BarbodH/ampere/components/chassis/v1.1/chassis.stl

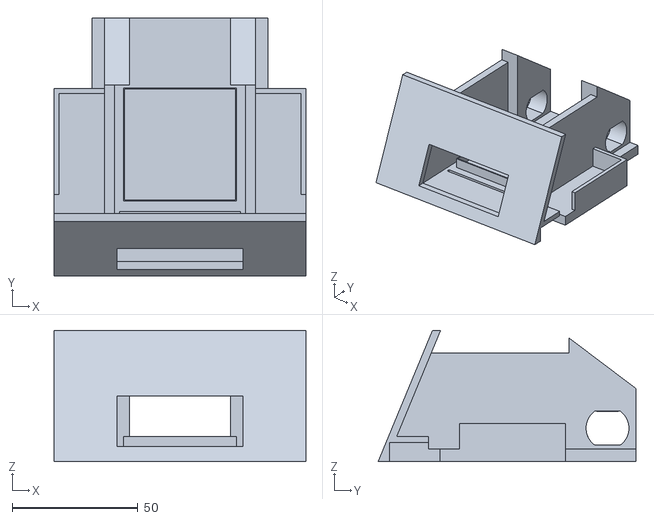
[picture p16: CAD file, 2023-03-18, an earlier design]
components/chassis/v1.1/chassis.stl
100.0 x 102.3 x 52.0
